MahimanaGIT/automatic_curtain/docs/latex/indicator_8cpp__incl.pdf

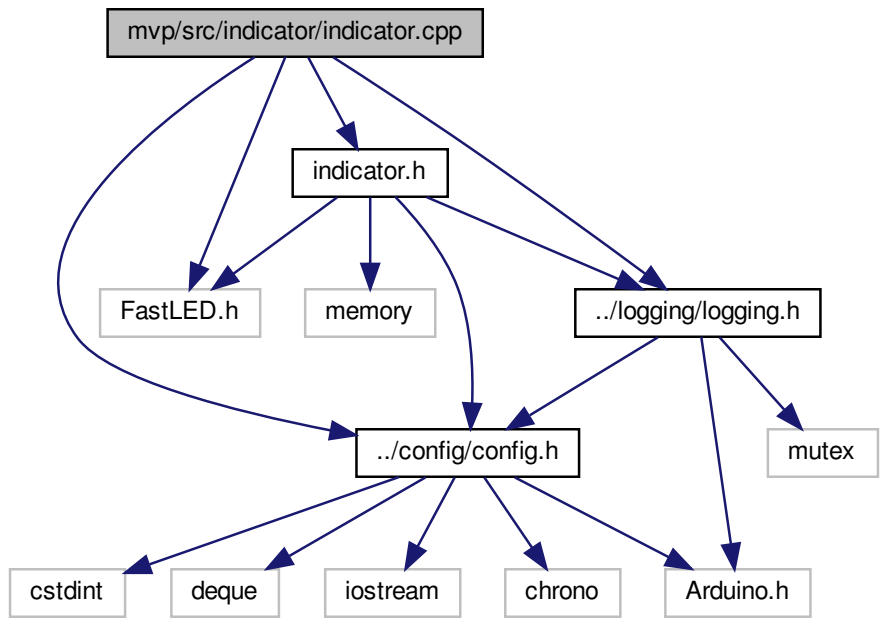
[picture p10: figure]
mvp/src/indicator/indicator.cpp; indicator.h; FastLED.h; ../config/config.h; memory; ../logging/logging.h; cstdint; deque; iostream; chrono; Arduino.h; mutex
