MahimanaGIT/automatic_curtain/docs/latex/indicator_8h__incl.pdf

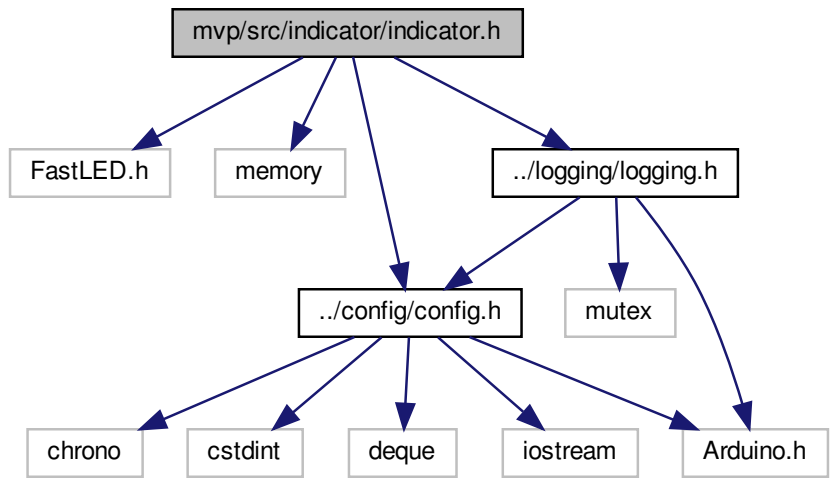
[picture p11: figure]
mvp/src/indicator/indicator.h; FastLED.h; memory; ../config/config.h; ../logging/logging.h; chrono; cstdint; deque; iostream; Arduino.h; mutex
