MahimanaGIT/automatic_curtain/docs/latex/logging_8cpp__incl.pdf

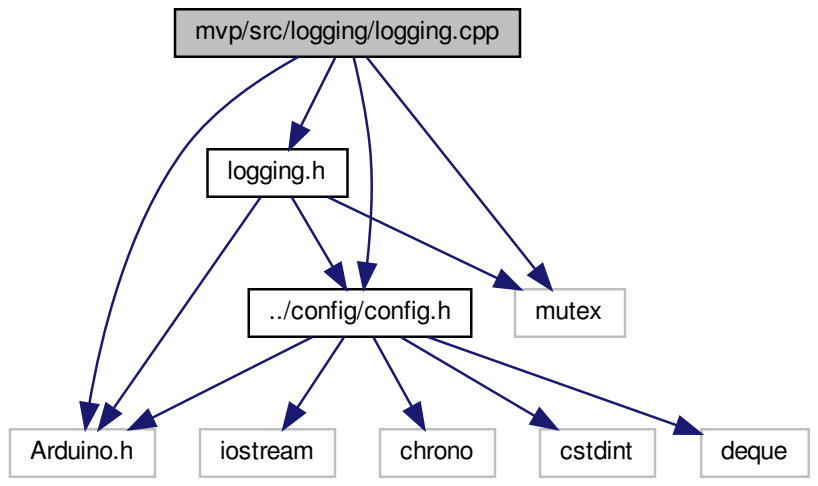
[picture p12: figure]
mvp/src/logging/logging.cpp; logging.h; Arduino.h; ../config/config.h; mutex; iostream; chrono; cstdint; deque
