MahimanaGIT/automatic_curtain/docs/latex/logging_8h__incl.pdf

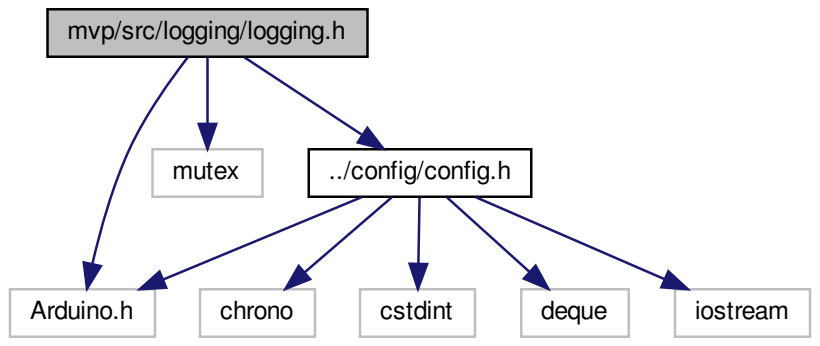
[picture p13: figure]
mvp/src/logging/logging.h; Arduino.h; mutex; ../config/config.h; chrono; cstdint; deque; iostream
