MahimanaGIT/automatic_curtain/docs/latex/motor__driver_8h__dep__incl.pdf

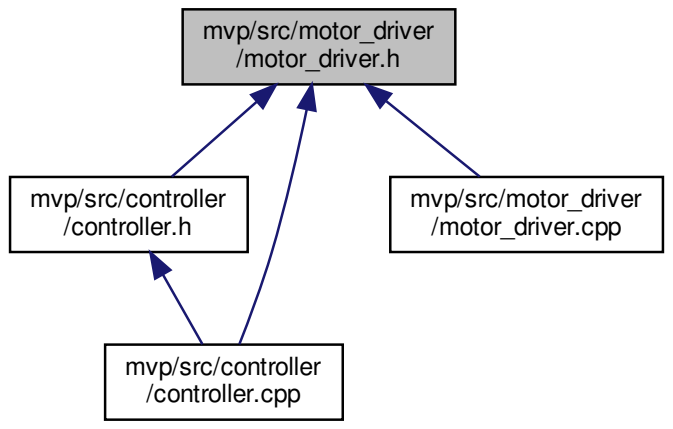
[picture p14: figure]
mvp/src/motor_driver /motor_driver.h; mvp/src/controller /controller.h; mvp/src/controller /controller.cpp; mvp/src/motor_driver /motor_driver.cpp
