MahimanaGIT/automatic_curtain/docs/latex/motor__driver_8h__incl.pdf

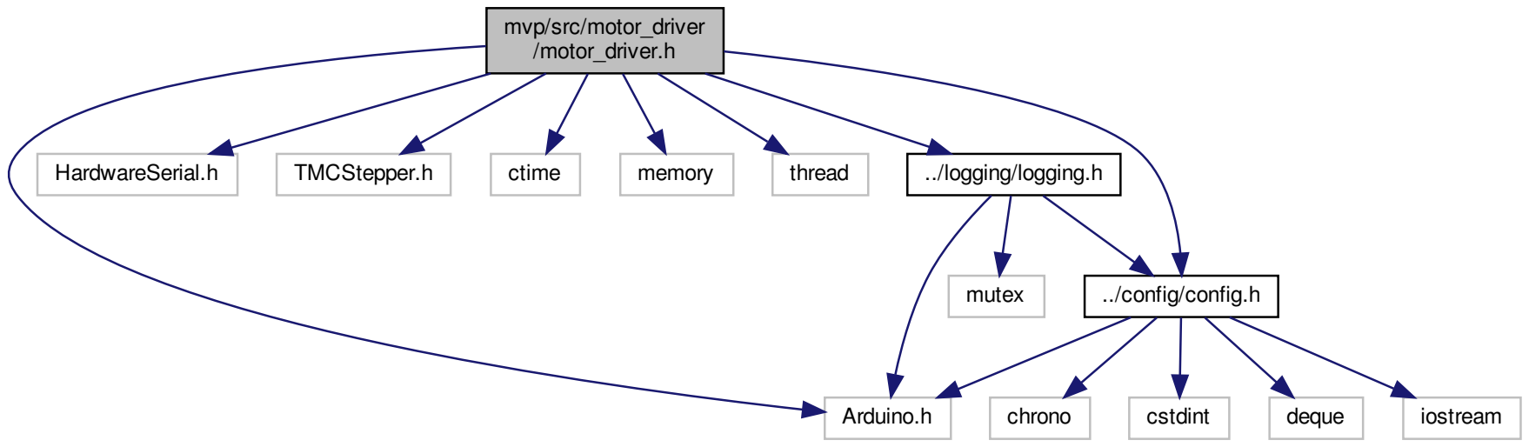
[picture p15: figure]
mvp/src/motor_driver /motor_driver.h; Arduino.h; HardwareSerial.h; TMCStepper.h; ctime; memory; thread; ../config/config.h; ../logging/logging.h; chrono; cstdint; deque; iostream; mutex
