MahimanaGIT/automatic_curtain/docs/latex/storage_8cpp__incl.pdf

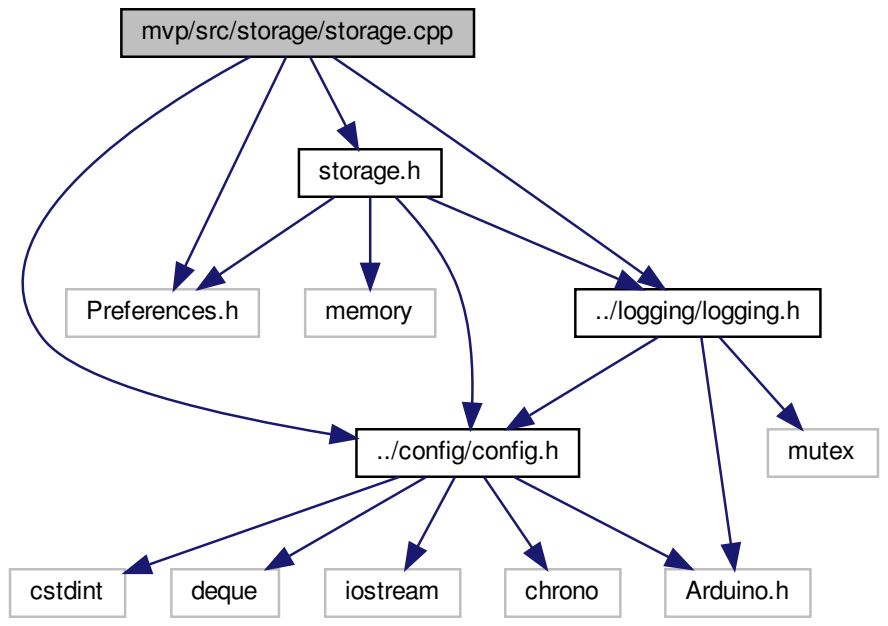
[picture p16: figure]
mvp/src/storage/storage.cpp; storage.h; Preferences.h; ../config/config.h; memory; ../logging/logging.h; cstdint; deque; iostream; chrono; Arduino.h; mutex
