MahimanaGIT/automatic_curtain/docs/latex/storage_8h__incl.pdf

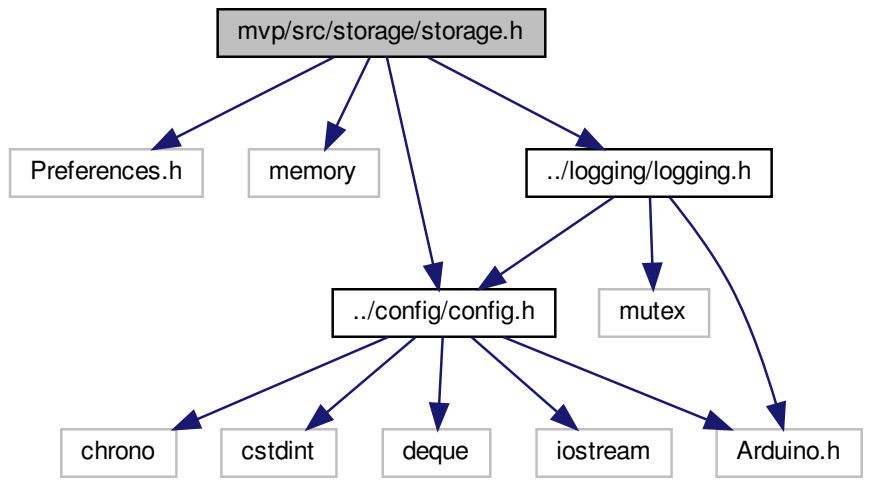
[picture p17: figure]
mvp/src/storage/storage.h; Preferences.h; memory; ../config/config.h; ../logging/logging.h; chrono; cstdint; deque; iostream; Arduino.h; mutex
