MahimanaGIT/automatic_curtain/docs/latex/indicator_8h__dep__incl.pdf

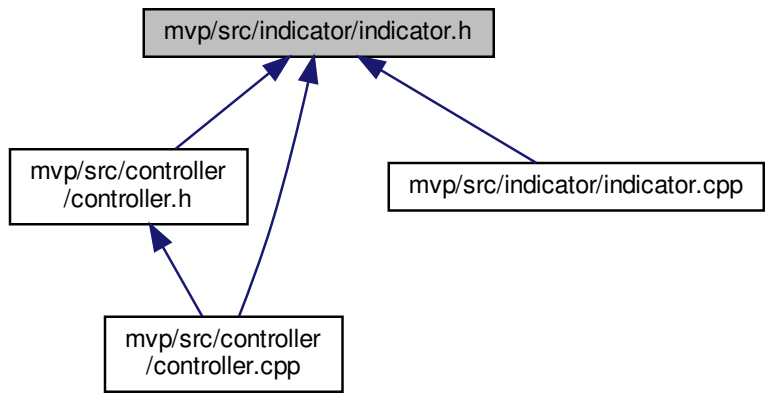
[picture p36: figure]
mvp/src/indicator/indicator.h; mvp/src/controller /controller.h; mvp/src/controller /controller.cpp; mvp/src/indicator/indicator.cpp
