MahimanaGIT/automatic_curtain/docs/latex/storage_8h__dep__incl.pdf

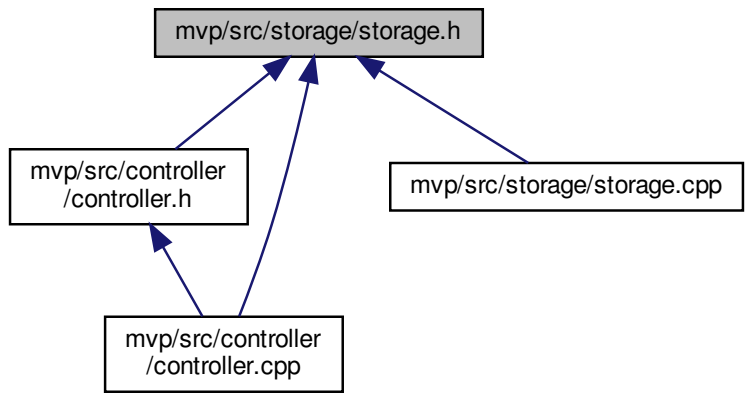
[picture p37: figure]
mvp/src/storage/storage.h; mvp/src/controller /controller.h; mvp/src/controller /controller.cpp; mvp/src/storage/storage.cpp
