MahimanaGIT/automatic_curtain/docs/classAlexaInteraction__coll__graph.png

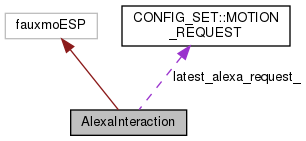
docs/classAlexaInteraction__coll__graph.png
