MahimanaGIT/automatic_curtain/docs/classConnectivity__coll__graph.png

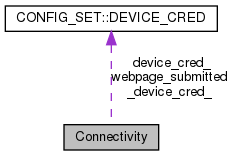
docs/classConnectivity__coll__graph.png
