MahimanaGIT/automatic_curtain/docs/classConnectivity_a0029e5f1650cb0152256d89595941e6a_cgraph.png

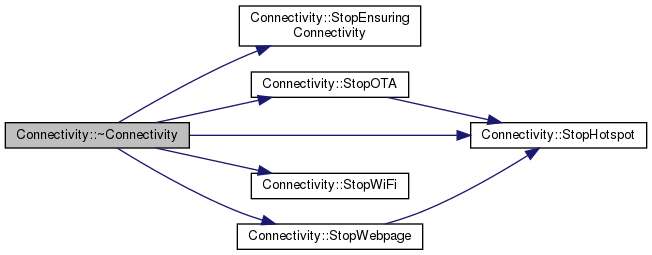
docs/classConnectivity_a0029e5f1650cb0152256d89595941e6a_cgraph.png
