MahimanaGIT/automatic_curtain/docs/classController__coll__graph.png

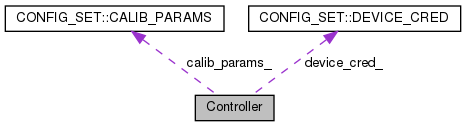
docs/classController__coll__graph.png
