MahimanaGIT/automatic_curtain/docs/classController_a431dc67f69757e96cfc9b42454c71097_cgraph.png

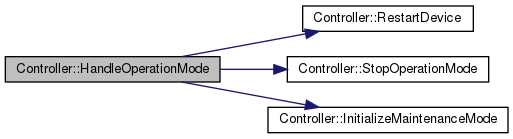
docs/classController_a431dc67f69757e96cfc9b42454c71097_cgraph.png
