MahimanaGIT/automatic_curtain/docs/classController_a4705ffb61d722e4916ba0d279dc27395_cgraph.png

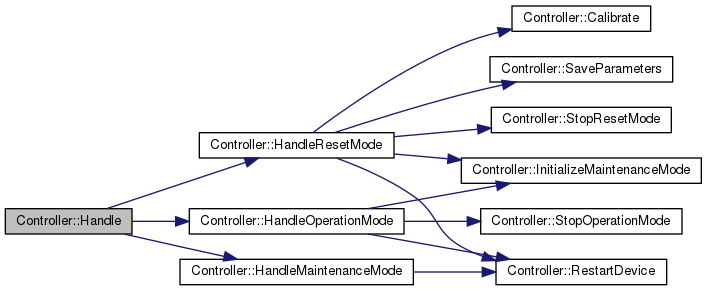
docs/classController_a4705ffb61d722e4916ba0d279dc27395_cgraph.png
