MahimanaGIT/automatic_curtain/docs/classController_ae512c48c1ebafb35c90948835361cf0c_cgraph.png

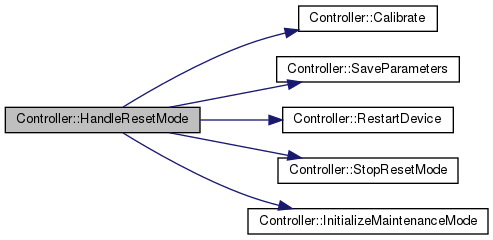
docs/classController_ae512c48c1ebafb35c90948835361cf0c_cgraph.png
