MahimanaGIT/automatic_curtain/docs/classMotorDriver__coll__graph.png

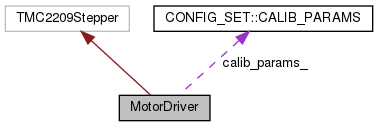
docs/classMotorDriver__coll__graph.png
