MahimanaGIT/automatic_curtain/docs/classMotorDriver_a534f4ca22b5dcffc9e40aafef09c76e5_cgraph.png

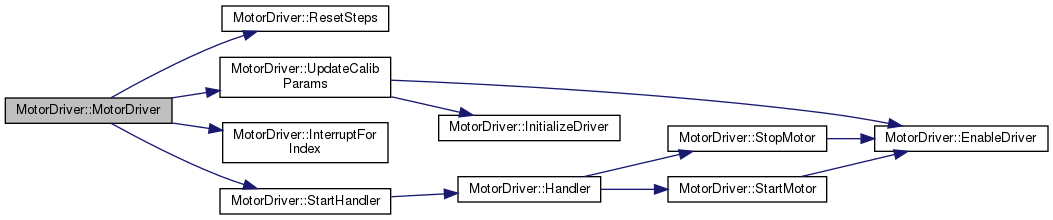
docs/classMotorDriver_a534f4ca22b5dcffc9e40aafef09c76e5_cgraph.png
