MahimanaGIT/automatic_curtain/docs/dir_1fcd52993bfdb54c2f03095b42eaa54f_dep.png

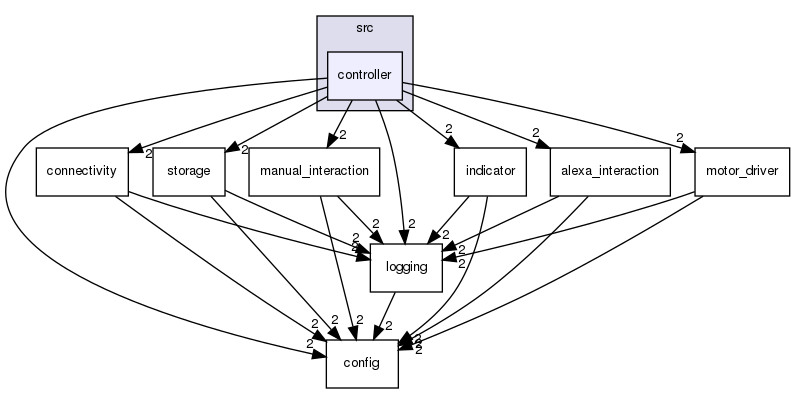
docs/dir_1fcd52993bfdb54c2f03095b42eaa54f_dep.png
