MahimanaGIT/automatic_curtain/docs/dir_68ab534310816d2c85c9b0933ced4ba8_dep.png

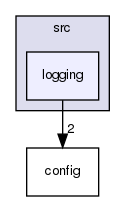
docs/dir_68ab534310816d2c85c9b0933ced4ba8_dep.png
