MahimanaGIT/automatic_curtain/docs/dir_5367f51a44270b849210ec03c27c9d7e_dep.png

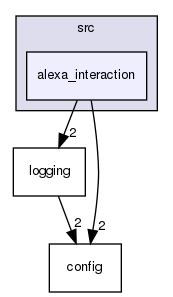
docs/dir_5367f51a44270b849210ec03c27c9d7e_dep.png
