MahimanaGIT/automatic_curtain/docs/dir_42554edaae5a8a80938acd2a943862bd_dep.png

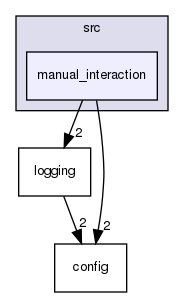
docs/dir_42554edaae5a8a80938acd2a943862bd_dep.png
