MahimanaGIT/automatic_curtain/docs/dir_57399f48e23ae7599baa28025749db70_dep.png

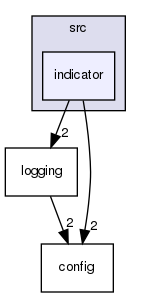
docs/dir_57399f48e23ae7599baa28025749db70_dep.png
