MahimanaGIT/automatic_curtain/docs/dir_36038656d9a800729273bcb331212d4a_dep.png

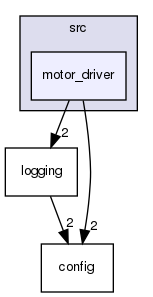
docs/dir_36038656d9a800729273bcb331212d4a_dep.png
