MahimanaGIT/automatic_curtain/docs/dir_a486437a11779643a8456ad4066f1106_dep.png

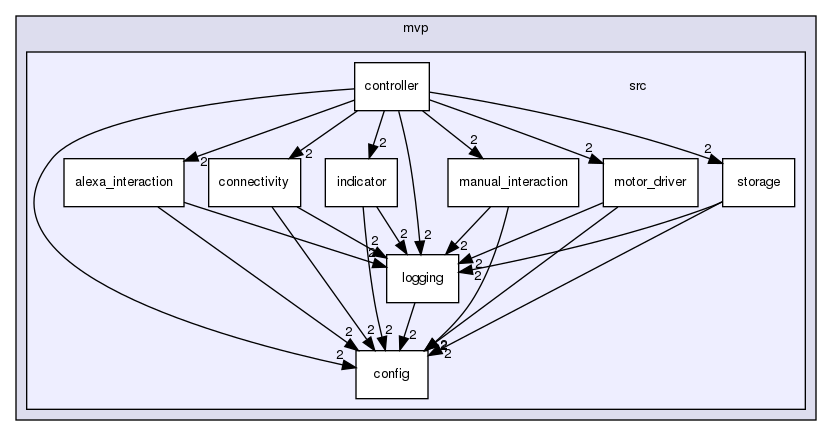
docs/dir_a486437a11779643a8456ad4066f1106_dep.png
