MahimanaGIT/automatic_curtain/docs/latex/controller_8h__incl.pdf

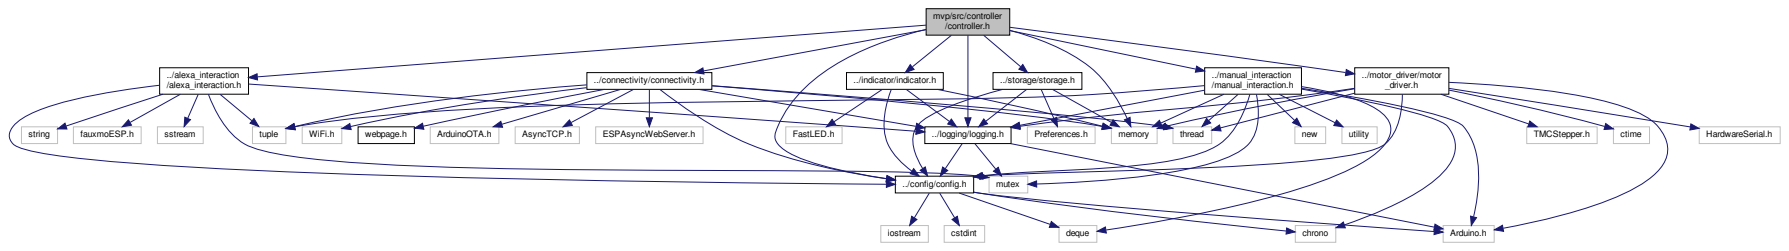
[picture p67: page 1]
memory; ../alexa_interaction /alexa_interaction.h; ../config/config.h; ../logging/logging.h; ../connectivity/connectivity.h; ../indicator/indicator.h; ../manual_interaction; /manual_interaction.h; ../motor_driver/motor _driver.h ../storage/storage.h; mutex; string; fauxmoESP.h; sstream; tuple; iostream; cstdint; deque; chrono; Arduino.h; WiFi.h; webpage.h; ArduinoOTA.h; AsyncTCP.h; ESPAsyncWebServer.h; FastLED.h; Preferences.h; thread; new; utility; TMCStepper.h; ctime; HardwareSerial.h

mvp/src/controller
/controller.h
