MahimanaGIT/automatic_curtain/docs/latex/logging_8h__dep__incl.pdf

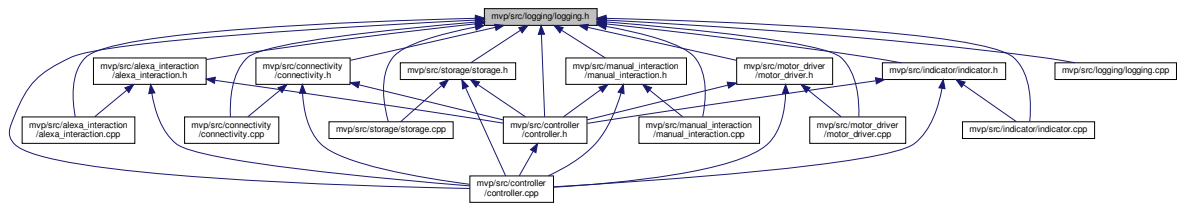
[picture p68: page 1]
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

mvp/src/logging/logging.h

mvp/src/connectivity
/connectivity.h

mvp/src/storage/storage.h

mvp/src/indicator/indicator.h

mvp/src/logging/logging.cpp

/connectivity.cpp

mvp/src/storage/storage.cpp

mvp/src/controller
/controller.h

mvp/src/indicator/indicator.cpp

/controller.cpp
