MahimanaGIT/automatic_curtain/docs/latex/motor__driver_8cpp__incl.pdf

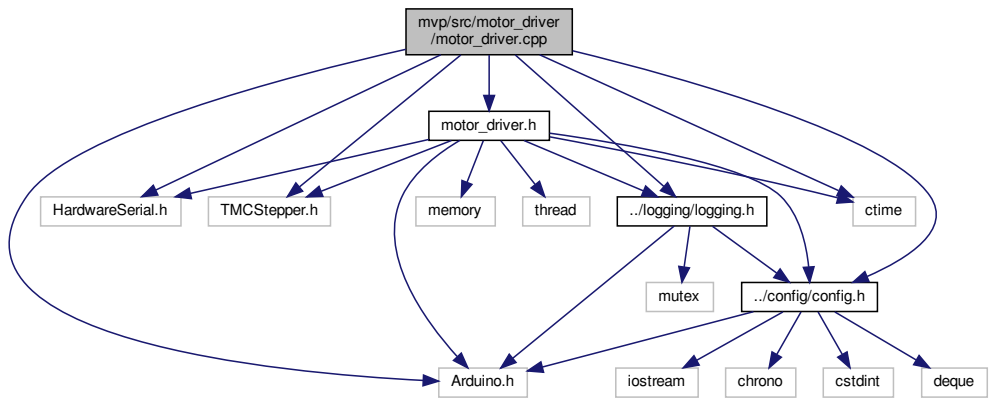
[picture p69: page 1]
mvp/src/motor_driver /motor_driver.cpp; motor_driver.h; Arduino.h; HardwareSerial.h; TMCStepper.h; ctime; ../config/config.h; memory; thread; ../logging/logging.h; iostream; chrono; cstdint; deque; mutex
